pierreca/SparkLedMatrix/case/front_plate.scad

use <case_elements.scad>;
include <case_dimensions.scad>;

$fs = 0.1;

projection (cut=false)
	fb_plate(0,0);
