pierreca/SparkLedMatrix/SparkCode/LedControl.h

#include "application.h"
/*
    Port of Eberhard Fahle's LedControl library for controlling the
    MAX7219/MAX7221 for the Spark Core.
*/
/*
 *    LedControl.h - A library for controling Leds with a MAX7219/MAX7221
 *    Copyright (c) 2007 Eberhard Fahle
 *
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
 *    This permission notice shall be included in all copies or
 *    substantial portions of the Software.
 *
 *    THE SOFTWARE IS PROVIDED "AS IS", WITHOUT WARRANTY OF ANY KIND,
 *    EXPRESS OR IMPLIED, INCLUDING BUT NOT LIMITED TO THE WARRANTIES
 *    OF MERCHANTABILITY, FITNESS FOR A PARTICULAR PURPOSE AND
 *    NONINFRINGEMENT. IN NO EVENT SHALL THE AUTHORS OR COPYRIGHT
 *    HOLDERS BE LIABLE FOR ANY CLAIM, DAMAGES OR OTHER LIABILITY,
 *    WHETHER IN AN ACTION OF CONTRACT, TORT OR OTHERWISE, ARISING
 *    FROM, OUT OF OR IN CONNECTION WITH THE SOFTWARE OR THE USE OR
 *    OTHER DEALINGS IN THE SOFTWARE.
 */


/*
 * Segments to be switched on for characters and digits on
 * 7-Segment Displays
 */
const static byte charTable[128] = {
    126,48,109,121,51,91,95,112,
    127,123,119,31,13,61,79,71,
    0,0,0,0,0,0,0,0,
    0,0,0,0,0,0,0,0,
    0,0,0,0,0,0,0,0,
    0,0,0,0,128,1,128,0,
    126,48,109,121,51,91,95,112,
    127,123,0,0,0,0,0,0,
    0,119,31,13,61,79,71,0,
    55,0,0,0,14,0,0,0,
    103,0,0,0,0,0,0,0,
    0,0,0,0,0,0,0,8,
    0,119,31,13,61,79,71,0,
    55,0,0,0,14,0,0,0,
    103,0,0,0,0,0,0,0,
    0,0,0,0,0,0,0,0
};

//8x8 font
const static byte cp437_font [256] [8] = {
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
  { 0x44, 0x6C, 0x38, 0x10, 0x38, 0x6C, 0x44, 0x00 }, // 'x'
  { 0x9C, 0xBC, 0xA0, 0xA0, 0xFC, 0x7C, 0x00, 0x00 }, // 'y'
  { 0x4C, 0x64, 0x74, 0x5C, 0x4C, 0x64, 0x00, 0x00 }, // 'z'
  { 0x08, 0x08, 0x3E, 0x77, 0x41, 0x41, 0x00, 0x00 }, // '{'
  { 0x00, 0x00, 0x00, 0x77, 0x77, 0x00, 0x00, 0x00 }, // '|'
  { 0x41, 0x41, 0x77, 0x3E, 0x08, 0x08, 0x00, 0x00 }, // '}'
  { 0x02, 0x03, 0x01, 0x03, 0x02, 0x03, 0x01, 0x00 }, // '~'
  { 0x70, 0x78, 0x4C, 0x46, 0x4C, 0x78, 0x70, 0x00 }, // 0x7F
  { 0x0E, 0x9F, 0x91, 0xB1, 0xFB, 0x4A, 0x00, 0x00 }, // 0x80
  { 0x3A, 0x7A, 0x40, 0x40, 0x7A, 0x7A, 0x40, 0x00 }, // 0x81
  { 0x38, 0x7C, 0x54, 0x55, 0x5D, 0x19, 0x00, 0x00 }, // 0x82
  { 0x02, 0x23, 0x75, 0x55, 0x55, 0x7D, 0x7B, 0x42 }, // 0x83
  { 0x21, 0x75, 0x54, 0x54, 0x7D, 0x79, 0x40, 0x00 }, // 0x84
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
};  //  end of cp437_font


struct ColumnsTable {
    byte *columns;
    int columnsCount;
};

class LedControl {
 private :
    /* The array for shifting the data to the devices */
    byte spidata[16];
    /* Send out a single command to the device */
    void spiTransfer(int addr, byte opcode, byte data);

    /* We keep track of the led-status for all 8 devices in this array */
    byte status[64];
    /* Data is shifted out of this pin*/
    int SPI_MOSI;
    /* The clock is signaled on this pin */
    int SPI_CLK;
    /* This one is driven LOW for chip selectzion */
    int SPI_CS;
    /* The maximum number of devices we use */
    int maxDevices;
    uint8_t maxCols;
    uint8_t colsPerDisplay = 8;

 public:
    /*
     * Create a new controler
     * Params :
     * dataPin		pin on the Arduino where data gets shifted out
     * clockPin		pin for the clock
     * csPin		pin for selecting the device
     * numDevices	maximum number of devices that can be controled
     */
    LedControl(int dataPin, int clkPin, int csPin, int numDevices=1);

    /*
     * Gets the number of devices attached to this LedControl.
     * Returns :
     * int	the number of devices on this LedControl
     */
    int getDeviceCount();

    /*
     * Set the shutdown (power saving) mode for the device
     * Params :
     * addr	The address of the display to control
     * status	If true the device goes into power-down mode. Set to false
     *		for normal operation.
     */
    void shutdown(int addr, bool status);

    /*
     * Set the number of digits (or rows) to be displayed.
     * See datasheet for sideeffects of the scanlimit on the brightness
     * of the display.
     * Params :
     * addr	address of the display to control
     * limit	number of digits to be displayed (1..8)
     */
    void setScanLimit(int addr, int limit);

    /*
     * Set the brightness of the display.
     * Params:
     * addr		the address of the display to control
     * intensity	the brightness of the display. (0..15)
     */
    void setIntensity(int addr, int intensity);

    /*
     * Switch all Leds on the display off.
     * Params:
     * addr	address of the display to control
     */
    void clearDisplay(int addr);

    /*
     * Set the status of a single Led.
     * Params :
     * addr	address of the display
     * row	the row of the Led (0..7)
     * col	the column of the Led (0..7)
     * state	If true the led is switched on,
     *		if false it is switched off
     */
    void setLed(int addr, int row, int col, bool state);

    /*
     * Set all 8 Led's in a row to a new state
     * Params:
     * addr	address of the display
     * row	row which is to be set (0..7)
     * value	each bit set to 1 will light up the
     *		corresponding Led.
     */
    void setRow(int addr, int row, byte value);

    /*
     * Set all 8 Led's in a column to a new state
     * Params:
     * addr	address of the display
     * col	column which is to be set (0..7)
     * value	each bit set to 1 will light up the
     *		corresponding Led.
     */
    void setColumn(int addr, int col, byte value);

    /*
     * Display a hexadecimal digit on a 7-Segment Display
     * Params:
     * addr	address of the display
     * digit	the position of the digit on the display (0..7)
     * value	the value to be displayed. (0x00..0x0F)
     * dp	sets the decimal point.
     */
    void setDigit(int addr, int digit, byte value, bool dp);

    /*
     * Display a character on a 7-Segment display.
     * There are only a few characters that make sense here :
     *	'0','1','2','3','4','5','6','7','8','9','0',
     *  'A','b','c','d','E','F','H','L','P',
     *  '.','-','_',' '
     * Params:
     * addr	address of the display
     * digit	the position of the character on the display (0..7)
     * value	the character to be displayed.
     * dp	sets the decimal point.
     */
    void setChar(int addr, int digit, char value, bool dp);

    void setLetter (int addr, const byte c);

    void tweenLetters (int addr, const byte c1, const byte c2, int speed=100);

    // Added by @pierreca
    /*
     * Set text to be displayed on all screens (whitespace will not be trimmed: one letter per display)
     * Params:
     * message: string containing the text to be displayed
     * messageLength: Length of the message to be displayed
     */
    void setText(char *message, int messageLength);

    /*
     * Set text to be displayed on all screens and scroll it (whitespace will not be trimmed: one letter per display)
     * Params:
     * message: string containing the text to be displayed
     * messageLength: Length of the message to be displayed
     * speed: interval to use between each iteration of scrolling
     */
    void scrollText(char *message, int messageLength, int speed);

    /*
     * Build a table of columns based on the text and trim the whitespace between to columns to maximize the number of letters displayed.
     * Params:
     * message: string containing the text to process
     * messageLength: Length of the text to process
     * result: Table of columns to be displayed
     * addPadding: indicates whether whitespace should be added before and after the text to make scrolling look better.
     */
    void buildTrimmedText(char *message, int messageLength, ColumnsTable *result, bool addPadding = false);

    /*
     * Display a table of columns on all screens
     * Params:
     * trimmedTextColumns: table of columns to be displayed
     * scrollIndex: column index at which the text should be displayed
     */
    void displayTrimmedText(ColumnsTable *trimmedTextColumns, int scrollIndex);

    /*
     * Clear all displays
     */
    void clearAllDisplays();

    /*
     * returns the number of columns on all screens]
     */
    uint8_t getColumnsCount();
};
